Teslamax/BMC-Lite-HAT/hardware/KiCad/bmc-lite-hat.kicad_sch

## KiCad design hardware/KiCad/bmc-lite-hat.kicad_sch (2025-04-17, an earlier design)

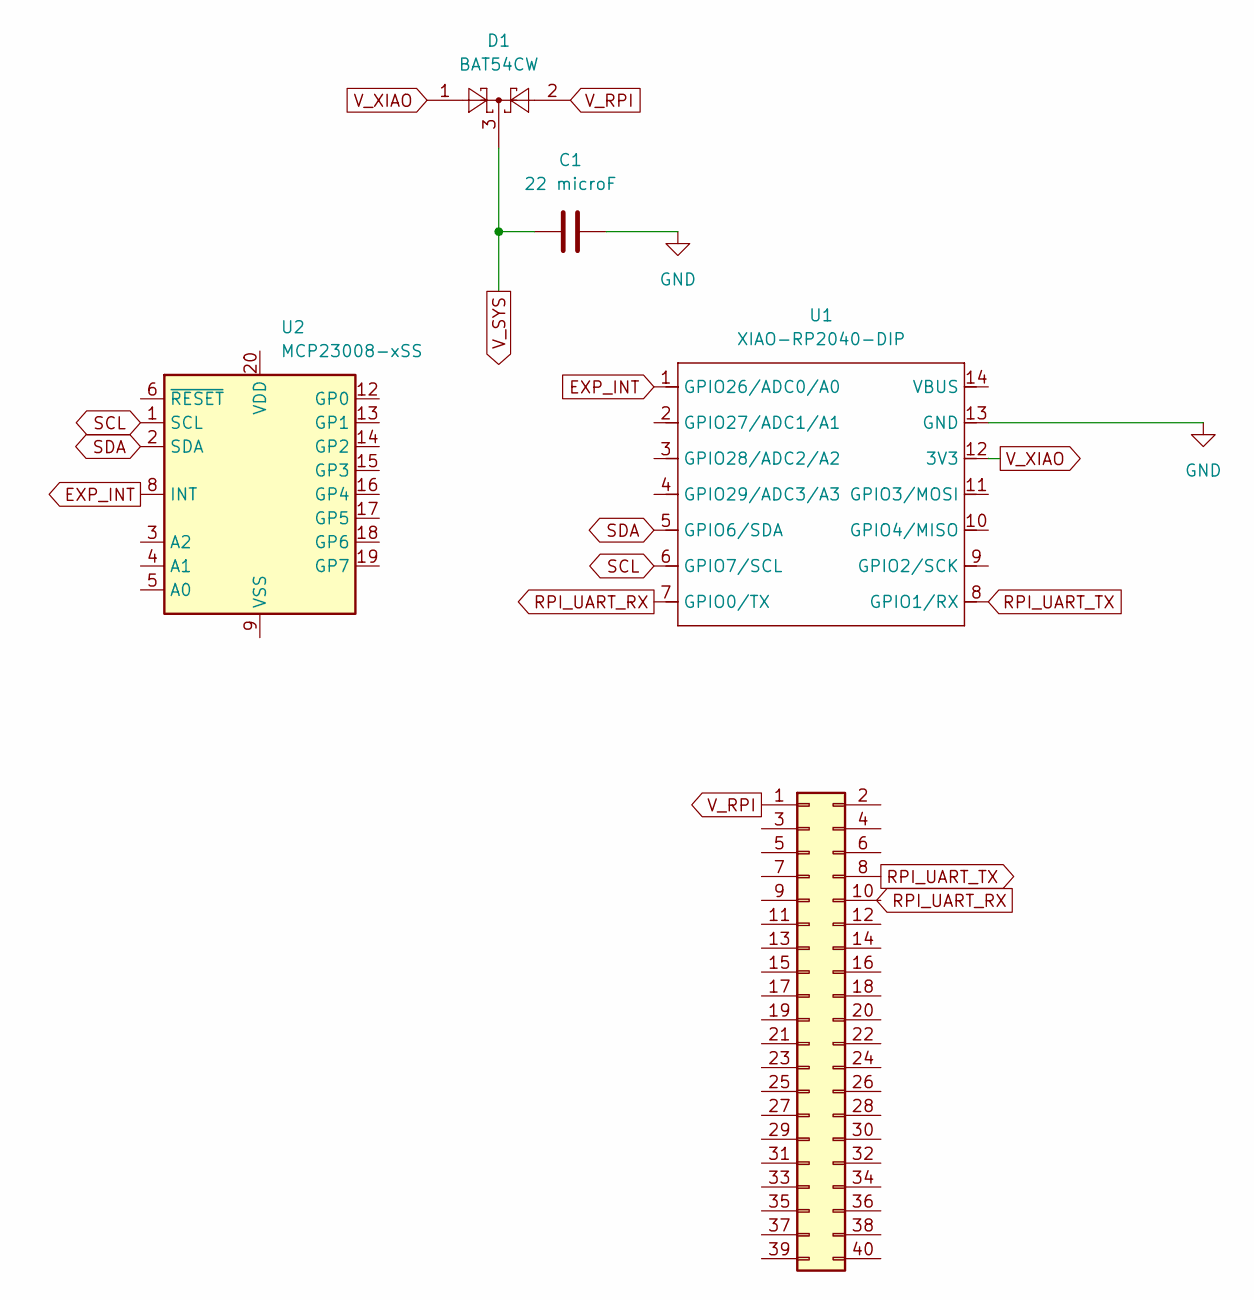
[picture p6: schematic bmc-lite-hat.kicad_sch]

Parts:
C1: 22 microF
D1: BAT54CW; SOT-323_SC-70
J1: Conn_02x20_Odd_Even
U1: XIAO-RP2040-DIP; MOUDLE14P-XIAO-DIP-SMD
U2: MCP23008-xSS; SSOP-20_5.3x7.2mm_P0.65mm

Connections:
EXP_INT: U1.1 (GPIO26/ADC0/A0), U2.8 (INT)
GND: C1.1, U1.13 (GND)
RPI_UART_RX: U1.7 (GPIO0/TX)
RPI_UART_TX: J1.8, U1.8 (GPIO1/RX)
SCL: U1.6 (GPIO7/SCL), U2.1 (SCL)
SDA: U1.5 (GPIO6/SDA), U2.2 (SDA)
V_RPI: D1.2, J1.1
V_SYS: C1.2, D1.3
V_XIAO: D1.1, U1.12 (3V3)
