Teslamax/BMC-Lite-HAT/firmware/BMC-Lite-HAT/src/uart_parser.h

#pragma once

#include <Arduino.h>
#include "status_led.h"

// Initializes the parser; call once in setup()
void initUARTParser();
// Call in loop() to do both UART→USB and USB→UART
void parseUART();

void initSerialInterfaces();

void pulseLed(uint8_t pin);

void markCdcActivity();
